XasWorks/Hexa-Bot/3DModels/GrabArm/BallSpacer.scad

difference() {
	cylinder(r = 10, h = 10);
	cylinder(r = 8, h = 11);
	translate([0, 0, 25 + 1]) sphere(r = 25);
}
