XasWorks/Hexa-Bot/3DModels/STL/Animation.scad

use <../Lib/NewHexGrid.scad>


echo("HexTranslation: " + test([0, 0, 0]));
