XasWorks/Hexa-Bot/3DModels/Various/QRCode/QRCode.scad

resize([23, 0, 2], auto=true)
surface("qrcodeWB.png");
cube([23, 23, 0.5]);
