XasWorks/Hexa-Bot/Code/ColorRecognitionsensor_ArduinoVersion_/ColorRecognitionsensor_ArduinoVersion_.ino

/*
// Sensor connection pins to Arduino are shown in comments

Color Sensor      Arduino
-----------      --------
 VCC               5V
 GND               GND
 s0                8
 s1                9
 s2                12
 s3                11
 OUT               10
 OE                GND
*/
const int s0 = 8;  
const int s1 = 9;  
const int s2 = 12;  
const int s3 = 11;  
const int out = 10;   


int red = 0;  
int green = 0;  
int blue = 0;  
    
void setup()   
{  
  Serial.begin(9600); 
  pinMode(s0, OUTPUT);  
  pinMode(s1, OUTPUT);  
  pinMode(s2, OUTPUT);  
  pinMode(s3, OUTPUT);  
  pinMode(out, INPUT);  
  digitalWrite(s0, HIGH);  
  digitalWrite(s1, HIGH);  
}  
    
void loop() // Display RGB and colors in the serial Monitor
{  
  color(); 
  Serial.print("R Intensity:");  
  Serial.print(red, DEC);  
  Serial.print(" G Intensity: ");  
  Serial.print(green, DEC);  
  Serial.print(" B Intensity : ");  
  Serial.print(blue, DEC);  
  

  if (red < blue && red < green && red < 9)
  {  
   Serial.println(" - (Red Color)");  
   }  

  else if (blue < red && blue < green && blue < 14)   
  {  
   Serial.println(" - (Blue Color)");  
  }  

  else if ( green < blue && green < 16)  
  {  
   Serial.println(" - (Green Color)");  
  } 
  
  else if (red > 20 && green > 20 && blue >20)
  {
    Serial.println(" - (Black Color)");
  }
  
  else{
  Serial.println();  
  }
  delay(1000); 
 }  
    
void color()  //Color reading
{    
  digitalWrite(s2, LOW);  
  digitalWrite(s3, LOW);  
  red = pulseIn(out, digitalRead(out) == HIGH ? LOW : HIGH);  
  digitalWrite(s3, HIGH);  
  blue = pulseIn(out, digitalRead(out) == HIGH ? LOW : HIGH);  
  digitalWrite(s2, HIGH);  
  green = pulseIn(out, digitalRead(out) == HIGH ? LOW : HIGH);  
}
