XasWorks/Hexa-Bot/Code/Movement/PrimitiveStepper.h

#ifndef _PRIMITIVE_STEPPER_H
#define _PRIMITIVE_STEPPER_H

#include <avr/io.h>
#include <util/atomic.h>
#include <math.h>
#include "../Updatable.h"


class PrimitiveStepper : Updatable {
protected:
	//Constructor for derived classes. Does not initialise any values!!
	PrimitiveStepper();

	//Port of the stepper motor
	volatile uint8_t *PORT;
	//Pin of the stepper motor. Stepping signals are issued at pin, dir signals at pin+1
	uint8_t pin;

	//Speed of the ISR. Required to set the stepping speed correctly.
	uint16_t updateFrequency;

	//Total steps the motor has made. Useful for absolute positioning.
	volatile int32_t currentSteps;
	//Steps the motor still has to make.
	float stepsToGo;

	//Steps per ISR Call.
	float stepSpeed;
	//Step buffer of the system. Not every ISR call will induce a Step, thusly, the rest has to be buffered.
	float stepBuffer;

	//Step the motor ONCE into the specified direction (0 == backwards, else forwards)
	void step(uint8_t dir);

public:

	//Main constructor of the Stepper motor. P is the port, p the first of the two pins required for the motor.
	//updateFrequency specifies the ISR speed that the motor runs on.
	PrimitiveStepper(volatile uint8_t *P, uint8_t pin,
			volatile uint16_t updateFrequency);

	//ISR Function to update the stepper motor (Stepping it when required)
	void update();

	//Set the speed in steps per Second. Primitive, not influenced by steps/mm.
	void setSpeed(uint16_t stepsPerSecond); //Move the motor by a certain amount of steps. Primitive, not influenced by steps/mm.
	//Reset the motor and abort all movements.
	void reset();

	void move(int32_t steps);
	//Wait for every motor move of this motor to finish.
	void flush();
};

#endif
