XasWorks/Hexa-Bot/Code/ComsCodes.h

/*
 * ComsCodes.h
 *
 *  Created on: Mar 18, 2016
 *      Author: xasin
 */

#ifndef CODE_COMSCODES_H_
#define CODE_COMSCODES_H_

#define COMS_SERVO 	1
#define COMS_IRDIST 2
#define COMS_BRIGHT 3

#endif /* CODE_COMSCODES_H_ */
