XasWorks/Hexa-Bot/Code/Modules/ModuleBasic.h

/*
 * Basic.h
 *
 *  Created on: Jan 15, 2016
 *      Author: xasin
 */

#ifndef CODE_MODULES_MODULEBASIC_H_
#define CODE_MODULES_MODULEBASIC_H_

namespace Module {

	class Basic {
	public:
		Basic();

		virtual void execute();
	};

}

#endif /* CODE_MODULES_MODULEBASIC_H_ */
